ElKinoflop/Izitafauxty/dxf/2 - Accent.dxf

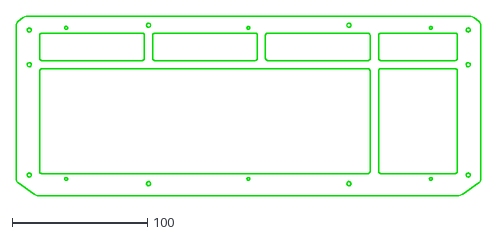
[picture p20: CAD file, 2024-11-16]
dxf/2 - Accent.dxf
343.2 x 132.4
